atoomnetmarc/WiFi-2-OIP-UI/Firmware/ESP32/src/config.cpp

/*

Copyright 2024-2026 Marc Ketel
SPDX-License-Identifier: Apache-2.0

*/

#include "config.h"

// WiFi configuration.
const char *ssid1 = WIFI1_SSID;
const char *password1 = WIFI1_PASSWORD;

// Another WiFi configuration.
const char *ssid2 = WIFI2_SSID;
const char *password2 = WIFI2_PASSWORD;

// OTA configuration.
const char *otapassword = OTA_PASSWORD;

// MQTT configuration.
const char *mqtt_host = MQTT_HOST;
const char *mqtt_user = MQTT_USER;
const char *mqtt_pass = MQTT_PASS;
const int mqtt_port = MQTT_PORT;
