atoomnetmarc/WiFi-2-OIP-UI/Firmware/Shared/instruction.h

/*

Copyright 2024-2026 Marc Ketel
SPDX-License-Identifier: Apache-2.0

*/

#ifndef instruction_h
#define instruction_h

#include <stdint.h>

#define INSTRUCTION_SYSTEMINFO_READ 0x01
#define INSTRUCTION_MESSAGE_WRITE   0x11

#endif
